ramirogm/balena-radio/diagrams/fritzing/finradio-v0.0.1.png

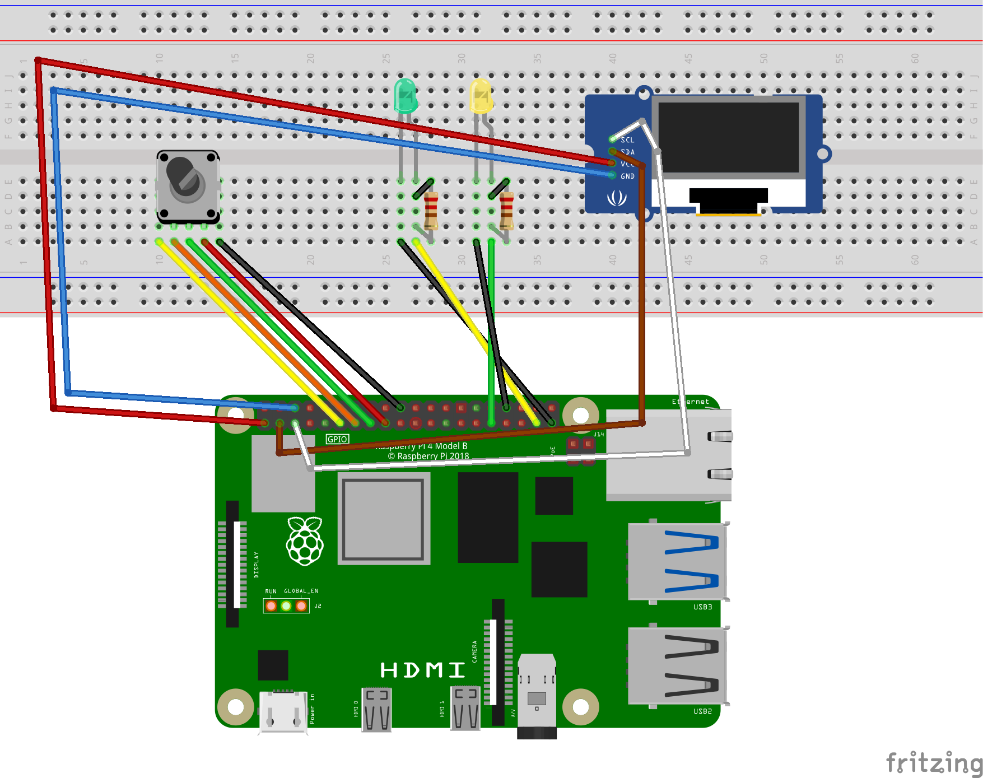
diagrams/fritzing/finradio-v0.0.1.png
