ramirogm/balena-radio/diagrams/rtl_tcp_alt.drawio.png

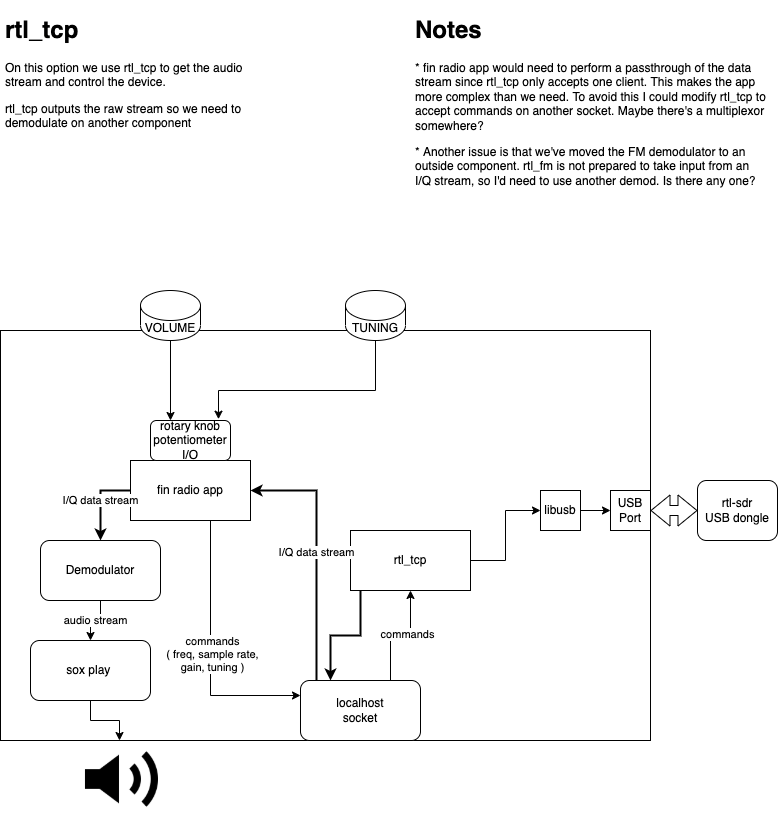
diagrams/rtl_tcp_alt.drawio.png
