ramirogm/balena-radio/i2c-display-test/index.js

// From https://www.npmjs.com/package/oled-i2c-bus
// this is for monochrome screens
// Mine ( https://articulo.mercadolibre.com.ar/MLA-743257264-pantalla-oled-display-096p-arduino-raspberry-arm-i2c-iic-se-_JM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 )
// is monochrome BUT it has the top +- 30 pixels yellow, and the rest blue

// To try:
// https://www.npmjs.com/package/oled-ssd1306-i2c


var i2c = require('i2c-bus'),
  i2cBus = i2c.openSync(1),
  oled = require('oled-i2c-bus');

var font = require('oled-font-5x7');

var opts = {
  width: 128,
  height: 64,
  address: 0x3C
};

var oled = new oled(i2cBus, opts);

// do cool oled things here
oled.turnOnDisplay();

oled.clearDisplay();

// draws 4 white pixels total
// format: [x, y, color]
// oled.drawPixel([
// 	[128, 1, 1],
// 	[128, 32, 1],
// 	[128, 16, 1],
// 	[64, 16, 1]
// ]);

// oled.fillRect(1, 1, 128, 64, 1);

// oled.drawLine(1, 1, 128, 32, 1);

// sets cursor to x = 1, y = 1
oled.setCursor(1, 1);
oled.writeString(font, 2, 'FinRadio', 1, false);

async function scanRange() {
    oled.setCursor(1, 30);
    for ( let i = 88.1; i < 108.0 ; i+=0.2) {
        oled.setCursor(1, 30);
        const msg = ( i < 100 ? " " : "" ) + i.toFixed(2) + " Mhz";
        oled.writeString(font, 2, msg, 1, false);
        await new Promise(resolve => setTimeout(resolve, 30));
    }    
    setInterval(() => scanRange(), 10 * 1000);
}

scanRange();
